cwoodall/artemis-synth/hardware/artemis-synth-v1.sch

## KiCad design hardware/artemis-synth-v1.sch (2013-07-03, an earlier design)

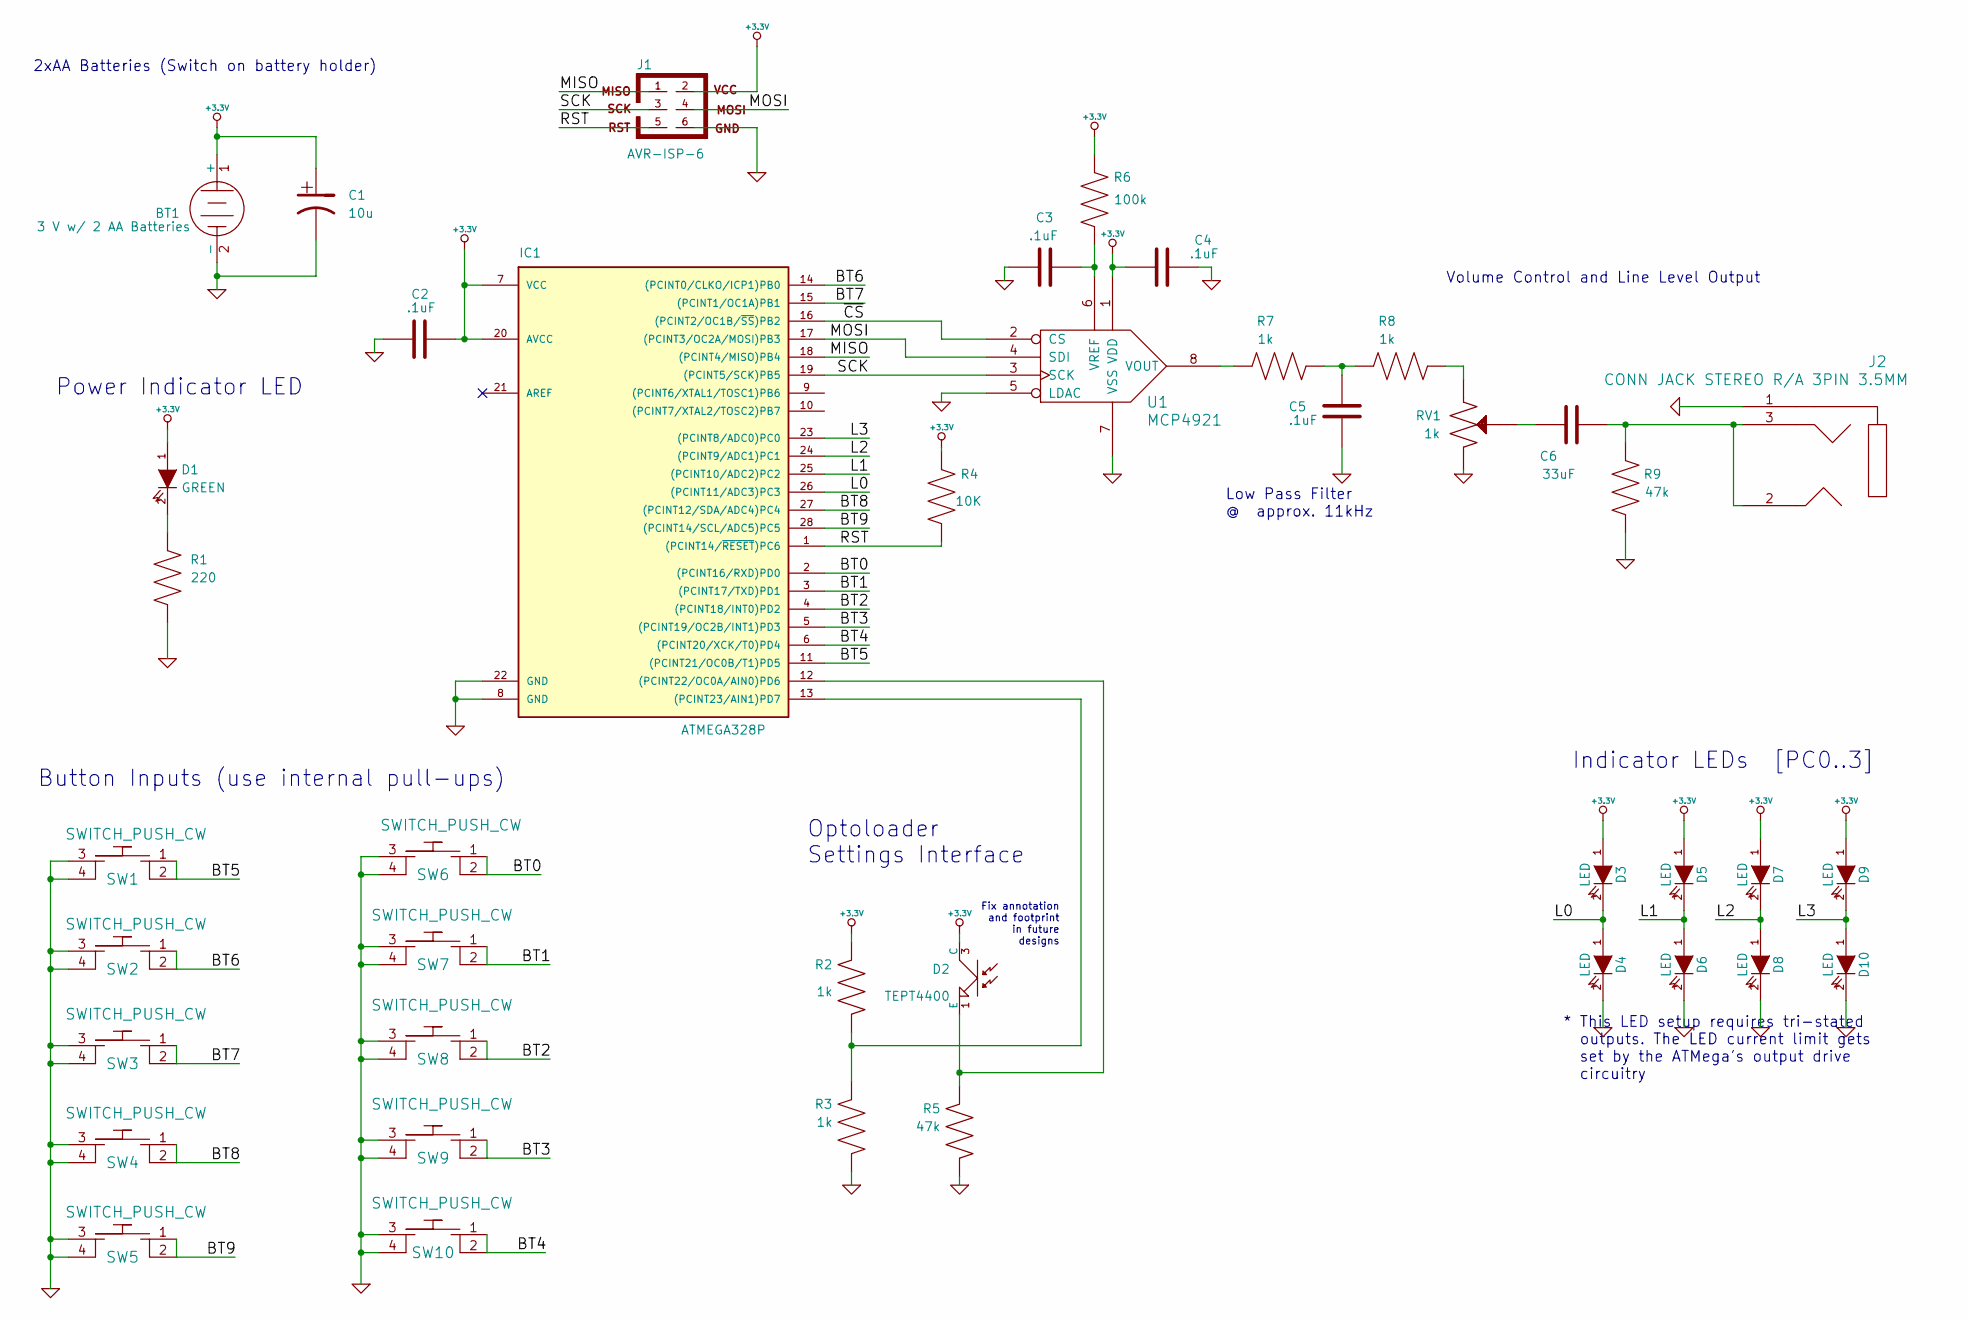
[picture p4: schematic artemis-synth-v1.sch]

Parts:
BT1: 3 V w/ 2 AA Batteries; 2PIN
C1: 10u
C2, C3, C4, C5: .1uF; C1
C6: 33uF; C1
D1: GREEN
D2: TEPT4400
D3, D4, D5, D6, D7, D8, D9, D10: LED; LED-5MM
IC1: ATMEGA328P; DIP-28__300
J1: AVR-ISP-6; pin_array_3x2
J2: CONN JACK STEREO R/A 3PIN 3.5MM; Manufacture Part Number SJ1-3523N
R1: 220
R2, R3, R7, R8: 1k
R4: 10K
R5, R9: 47k
R6: 100k
RV1: 1k
SW1, SW2, SW3, SW4, SW5, SW6, SW7, SW8, SW9, SW10: SWITCH_PUSH_CW; SparkFun-TACTILE-PTH-12MM
U1: MCP4921; DIP-8__300

Connections:
+3.3V: BT1.1 (+), C1.1, C2.1, C4.2, D1.1 (A), D2.3 (C), D3.1 (A), D5.1 (A), D7.1 (A), D9.1 (A), IC1.7 (VCC), IC1.20 (AVCC), J1.2, R2.1, R4.1, R6.1, U1.1 (VDD)
BT0: IC1.2 ((PCINT16/RXD)PD0), SW6.1, SW6.2
BT1: IC1.3 ((PCINT17/TXD)PD1), SW7.1, SW7.2
BT2: IC1.4 ((PCINT18/INT0)PD2), SW8.1, SW8.2
BT3: IC1.5 ((PCINT19/OC2B/INT1)PD3), SW9.1, SW9.2
BT4: IC1.6 ((PCINT20/XCK/T0)PD4), SW10.1, SW10.2
BT5: IC1.11 ((PCINT21/OC0B/T1)PD5), SW1.1, SW1.2
BT6: IC1.14 ((PCINT0/CLKO/ICP1)PB0), SW2.1, SW2.2
BT7: IC1.15 ((PCINT1/OC1A)PB1), SW3.1, SW3.2
BT8: IC1.27 ((PCINT12/SDA/ADC4)PC4), SW4.1, SW4.2
BT9: IC1.28 ((PCINT14/SCL/ADC5)PC5), SW5.1, SW5.2
GND: BT1.2 (-), C1.2, C2.2, C3.1, C4.1, C5.2, D4.2 (K), D6.2 (K), D8.2 (K), D10.2 (K), IC1.8 (GND), IC1.22 (GND), J1.6, J2.1, R1.2, R3.2, R5.2, R9.2, RV1.3, SW1.3, SW1.4, SW2.3, SW2.4, SW3.3, SW3.4, SW4.3, SW4.4, SW5.3, SW5.4, SW6.3, SW6.4, SW7.3, SW7.4, SW8.3, SW8.4, SW9.3, SW9.4, SW10.3, SW10.4, U1.5 (LDAC), U1.7 (VSS)
L0: D3.2 (K), D4.1 (A), IC1.26 ((PCINT11/ADC3)PC3)
L1: D5.2 (K), D6.1 (A), IC1.25 ((PCINT10/ADC2)PC2)
L2: D7.2 (K), D8.1 (A), IC1.24 ((PCINT9/ADC1)PC1)
L3: D9.2 (K), D10.1 (A), IC1.23 ((PCINT8/ADC0)PC0)
MISO: IC1.18 ((PCINT4/MISO)PB4), J1.1
MOSI: IC1.17 ((PCINT3/OC2A/MOSI)PB3), J1.4, U1.4 (SDI)
unnamed: C3.2, R6.2, U1.6 (VREF)
unnamed: C5.1, R7.2, R8.1
unnamed: C6.1, RV1.2
unnamed: C6.2, J2.2, J2.3, R9.1
unnamed: D1.2 (K), R1.1
unnamed: D2.1 (E), IC1.12 ((PCINT22/OC0A/AIN0)PD6), R5.1
unnamed: IC1.13 ((PCINT23/AIN1)PD7), R2.2, R3.1
unnamed: R7.1, U1.8 (VOUT)
unnamed: R8.2, RV1.1
RST: IC1.1 ((PCINT14/~RESET~)PC6), J1.5, R4.2
SCK: IC1.19 ((PCINT5/SCK)PB5), J1.3, U1.3 (SCK)
~CS: IC1.16 ((PCINT2/OC1B/~SS~)PB2), U1.2 (CS)

Notes on the sheet:
Optoloader Settings Interface
Indicator LEDs [PC0..3]
Button Inputs (use internal pull-ups)
2xAA Batteries (Switch on battery holder)
Fix annotation and footprint in future designs
* This LED setup requires tri-stated outputs. The LED current limit gets set by the ATMega's output drive circuitry
Low Pass Filter @ approx. 11kHz
Volume Control and Line Level Output
Power Indicator LED
