cwoodall/artemis-synth/hardware/artemis-synth.sch

## KiCad design hardware/artemis-synth.sch (2013-07-16, an earlier design)

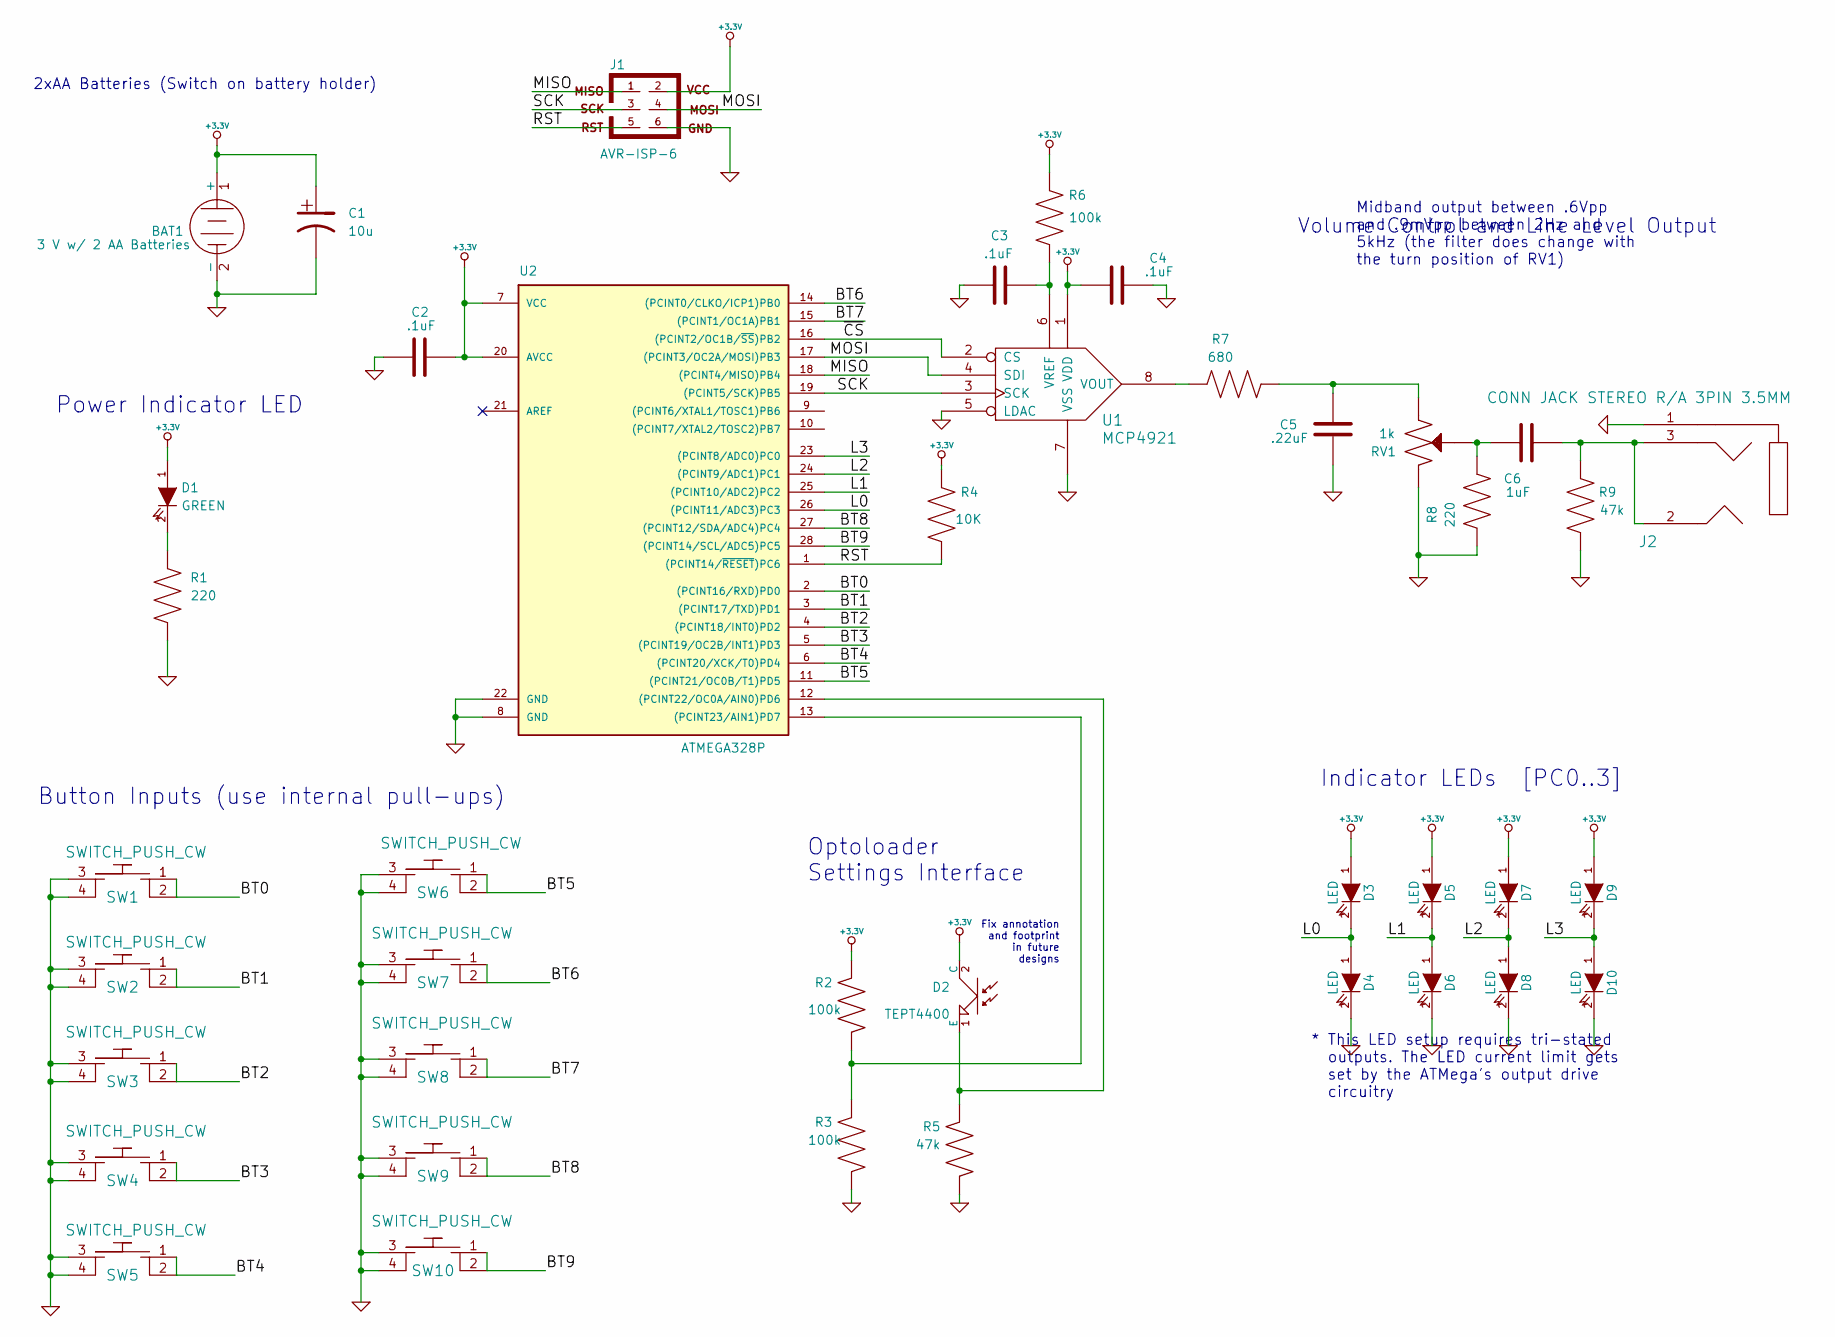
[picture p5: schematic artemis-synth.sch]

Parts:
BAT1: 3 V w/ 2 AA Batteries; 2PIN
C1: 10u; C1V8
C2, C3, C4: .1uF; C1
C5: .22uF; C1
C6: 1uF; C1
D1: GREEN; LED-3MM-CORRECTED
D2: TEPT4400; LED-3MM-CORRECTED
D3, D4, D5, D6, D7, D8, D9, D10: LED; LED-3MM-CORRECTED
J1: AVR-ISP-6; pin_array_3x2
J2: CONN JACK STEREO R/A 3PIN 3.5MM; 3-Pin; Manufacture Part Number SJ1-3523N
R1, R8: 220; R4
R2, R3, R6: 100k; R4
R4: 10K; R4
R5, R9: 47k; R4
R7: 680; R4
RV1: 1k; THUMBWHEEL_POT_3352T
SW1, SW2, SW3, SW4, SW5, SW6, SW7, SW8, SW9, SW10: SWITCH_PUSH_CW; SparkFun-TACTILE-PTH-12MM
U1: MCP4921; DIP-8__300
U2: ATMEGA328P; DIP-28__300

Connections:
+3.3V: BAT1.1 (+), C1.1, C2.1, C4.2, D1.1 (A), D2.2 (C), D3.1 (A), D5.1 (A), D7.1 (A), D9.1 (A), J1.2, R2.1, R4.1, R6.1, U1.1 (VDD), U2.7 (VCC), U2.20 (AVCC)
BT0: SW1.1, SW1.2, U2.2 ((PCINT16/RXD)PD0)
BT1: SW2.1, SW2.2, U2.3 ((PCINT17/TXD)PD1)
BT2: SW3.1, SW3.2, U2.4 ((PCINT18/INT0)PD2)
BT3: SW4.1, SW4.2, U2.5 ((PCINT19/OC2B/INT1)PD3)
BT4: SW5.1, SW5.2, U2.6 ((PCINT20/XCK/T0)PD4)
BT5: SW6.1, SW6.2, U2.11 ((PCINT21/OC0B/T1)PD5)
BT6: SW7.1, SW7.2, U2.14 ((PCINT0/CLKO/ICP1)PB0)
BT7: SW8.1, SW8.2, U2.15 ((PCINT1/OC1A)PB1)
BT8: SW9.1, SW9.2, U2.27 ((PCINT12/SDA/ADC4)PC4)
BT9: SW10.1, SW10.2, U2.28 ((PCINT14/SCL/ADC5)PC5)
GND: BAT1.2 (-), C1.2, C2.2, C3.1, C4.1, C5.2, D4.2 (K), D6.2 (K), D8.2 (K), D10.2 (K), J1.6, J2.1, R1.2, R3.2, R5.2, R8.1, R9.2, RV1.1, SW1.3, SW1.4, SW2.3, SW2.4, SW3.3, SW3.4, SW4.3, SW4.4, SW5.3, SW5.4, SW6.3, SW6.4, SW7.3, SW7.4, SW8.3, SW8.4, SW9.3, SW9.4, SW10.3, SW10.4, U1.5 (LDAC), U1.7 (VSS), U2.8 (GND), U2.22 (GND)
L0: D3.2 (K), D4.1 (A), U2.26 ((PCINT11/ADC3)PC3)
L1: D5.2 (K), D6.1 (A), U2.25 ((PCINT10/ADC2)PC2)
L2: D7.2 (K), D8.1 (A), U2.24 ((PCINT9/ADC1)PC1)
L3: D9.2 (K), D10.1 (A), U2.23 ((PCINT8/ADC0)PC0)
MISO: J1.1, U2.18 ((PCINT4/MISO)PB4)
MOSI: J1.4, U1.4 (SDI), U2.17 ((PCINT3/OC2A/MOSI)PB3)
unnamed: C3.2, R6.2, U1.6 (VREF)
unnamed: C5.1, R7.2, RV1.3
unnamed: C6.1, R8.2, RV1.2
unnamed: C6.2, J2.2, J2.3, R9.1
unnamed: D1.2 (K), R1.1
unnamed: D2.1 (E), R5.1, U2.12 ((PCINT22/OC0A/AIN0)PD6)
unnamed: R2.2, R3.1, U2.13 ((PCINT23/AIN1)PD7)
unnamed: R7.1, U1.8 (VOUT)
RST: J1.5, R4.2, U2.1 ((PCINT14/~RESET~)PC6)
SCK: J1.3, U1.3 (SCK), U2.19 ((PCINT5/SCK)PB5)
~CS: U1.2 (CS), U2.16 ((PCINT2/OC1B/~SS~)PB2)

Notes on the sheet:
Optoloader Settings Interface
Indicator LEDs [PC0..3]
Button Inputs (use internal pull-ups)
2xAA Batteries (Switch on battery holder)
Fix annotation and footprint in future designs
* This LED setup requires tri-stated outputs. The LED current limit gets set by the ATMega's output drive circuitry
Midband output between .6Vpp and .9mVpp between 2Hz and 5kHz (the filter does change with the turn position of RV1)
Volume Control and Line Level Output
Power Indicator LED
