cwoodall/artemis-synth/hardware/rev_a/artemis-synth-v1.sch

## KiCad design hardware/rev_a/artemis-synth-v1.sch (2012-07-02)

Schematic: artemis-synth-v1.sch

Parts:
BT1: BATTERY; 2PIN
C1, C5, C6, C7, C8, C11, C12, C13, C14: .1uF; C1
C2, C3: 22pF; C1
C9: .01uF; C1
C10: 10uF; SparkFun-CPOL-RADIAL-10UF-25V
D1, D2: 3V6; D4
D3, D4, D5, D6, D7, D8, D9, D10: LED; LED-5MM
IC1: ATMEGA328P; DIP-28__300
J1: USB_2; USB_B
J2: AVR-ISP-6; pin_array_3x2
R1: 2.2K; R4
R2, R3: 68; R4
R4: 47K; R4
R8: 10K; R4
R9: 100k; R4
R10: LDR; SIL-2
R11: 100K; R4
R12, R13: 1K; R4
R14: 1.5k; R4
R15, R16: 4.7; R4
RV1: 1K; THUMBWHEEL_POT_3352T
SP1: SPEAKER; 2PIN
SW2, SW3, SW4, SW5, SW6, SW7, SW8, SW9, SW10, SW11: SWITCH_PUSH_CW; SparkFun-TACTILE-PTH-12MM
U1: MCP4921; DIP-8__300
U2: TDA2722M; DIP-8__300
X1: 16MHz; HC-49V

Notes on the sheet:
Optoloader
LEDs [PC0..3]
Button Inputs (use internal pull-ups)
USBasp Bootloader Interface
16MHz Clock
2xAA Batteries (Switch on battery holder)
