cwoodall/artemis-synth/firmware/src/inst.c

#include "inst.h"
#include <avr/io.h>

// Sine_Table Wave
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
