cwoodall/artemis-synth/firmware/artemis-synth/inst.h

#ifndef _inst_h_
#define _inst_h_
#include <avr/io.h>
// Sine Wave
extern const uint16_t channelA[256];

//Square Wave
extern const uint16_t channelB[256];

//Sawtooth Wave
extern const uint16_t channelC[256];

// Triangle Wave
extern const uint16_t channelD[256];
#endif
